virgolibra/smart_office_project/flutter_smart_office_project/assets/title1.png

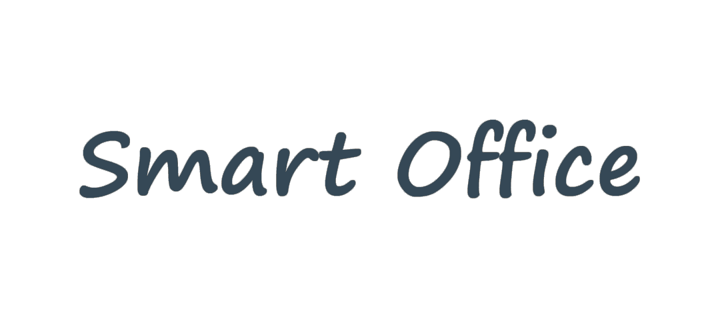
flutter_smart_office_project/assets/title1.png
