virgolibra/smart_office_project/images/Fusion/IRBoxMd1.jpg

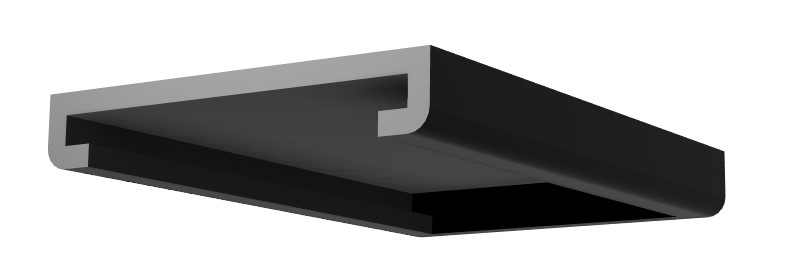
images/Fusion/IRBoxMd1.jpg
