virgolibra/smart_office_project/images/Fusion/IRBoxMd2.jpg

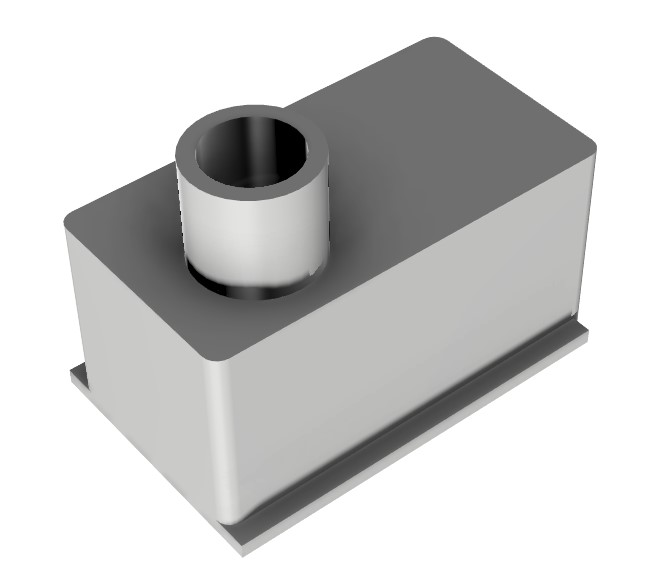
images/Fusion/IRBoxMd2.jpg
