virgolibra/smart_office_project/images/Fusion/IRBoxMd3.jpg

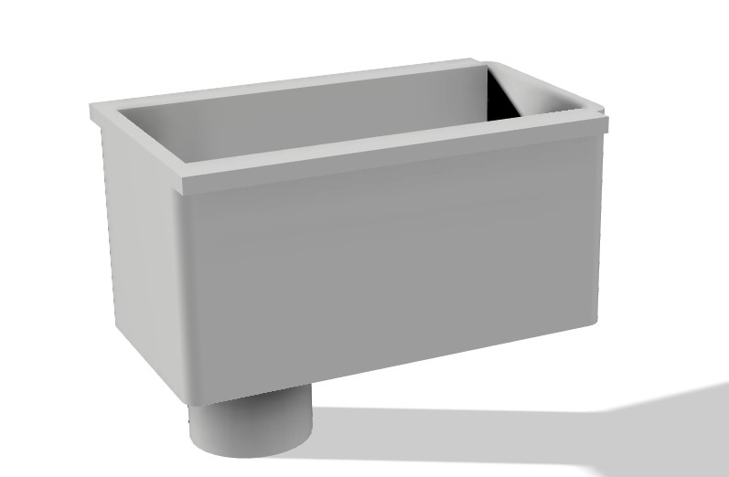
images/Fusion/IRBoxMd3.jpg
