virgolibra/smart_office_project/images/Fusion/IRBoxMd4.jpg

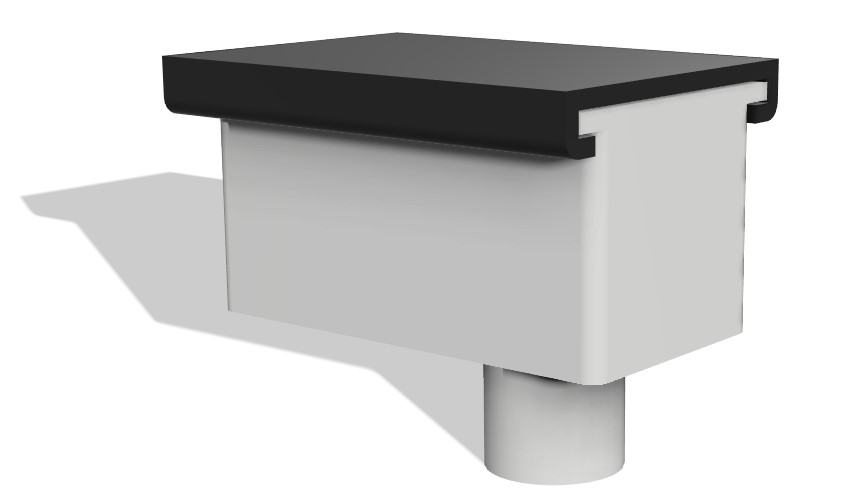
images/Fusion/IRBoxMd4.jpg
