virgolibra/smart_office_project/images/Fusion/IRBoxMd5.jpg

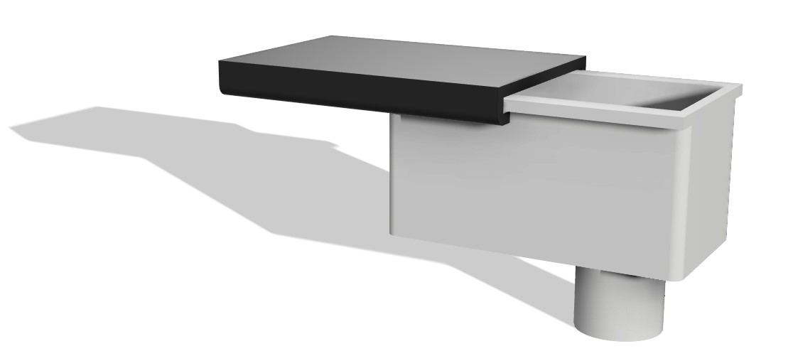
images/Fusion/IRBoxMd5.jpg
