virgolibra/smart_office_project/images/Fusion/IRBoxSd1.jpg

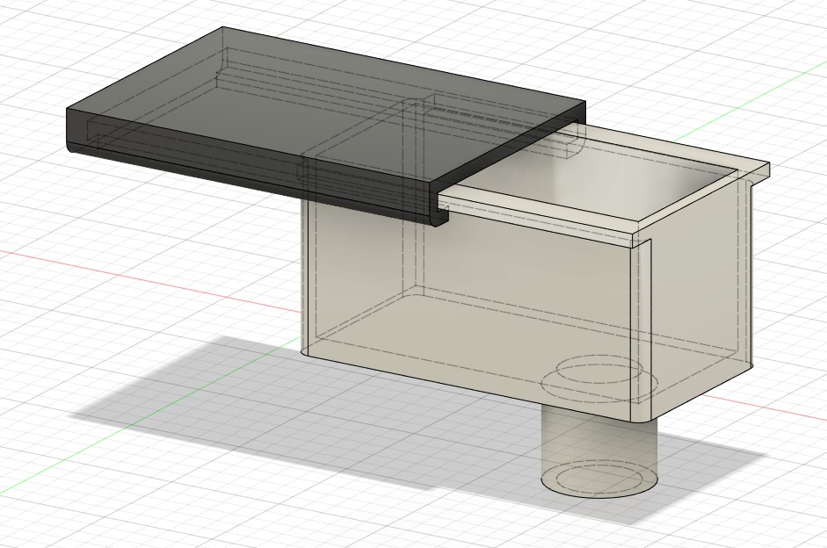
images/Fusion/IRBoxSd1.jpg
