virgolibra/smart_office_project/images/Fusion/IRBoxSk1.jpg

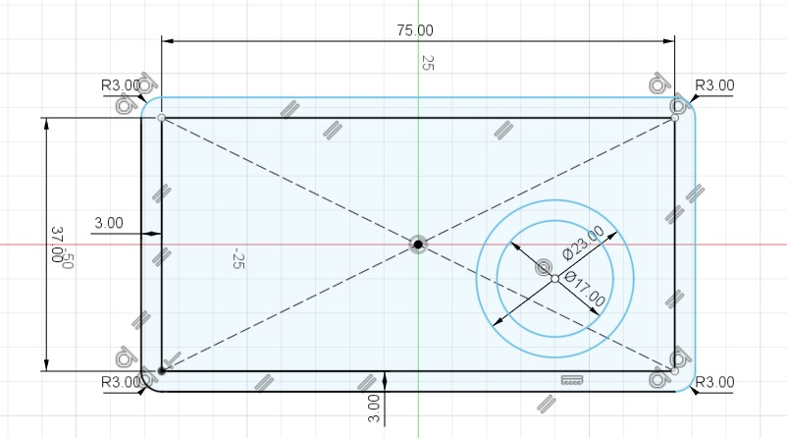
images/Fusion/IRBoxSk1.jpg
