virgolibra/smart_office_project/images/Fusion/IRBoxSk2.jpg

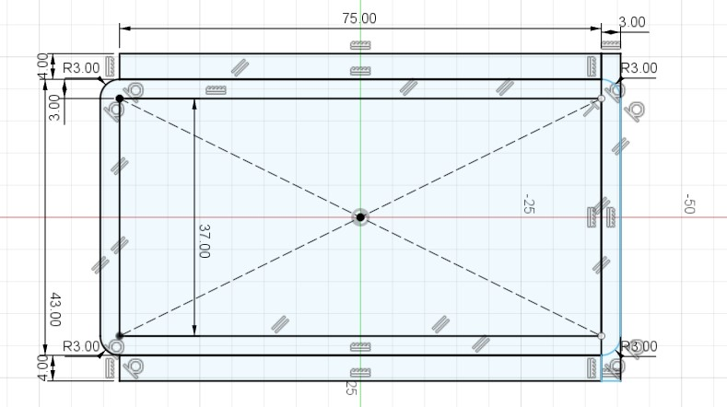
images/Fusion/IRBoxSk2.jpg
