virgolibra/smart_office_project/images/Fusion/IRBoxSk3.jpg

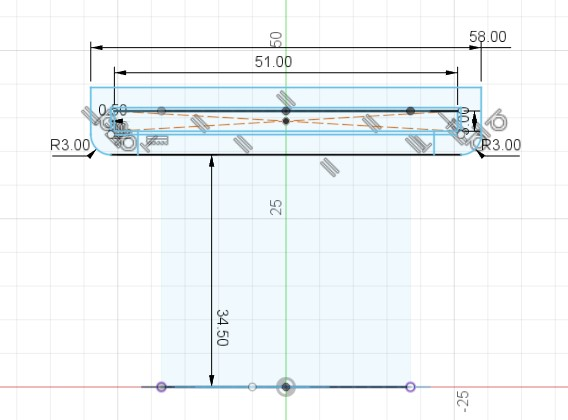
images/Fusion/IRBoxSk3.jpg
