virgolibra/smart_office_project/images/Fusion/RFID/RFIDRd1.jpg

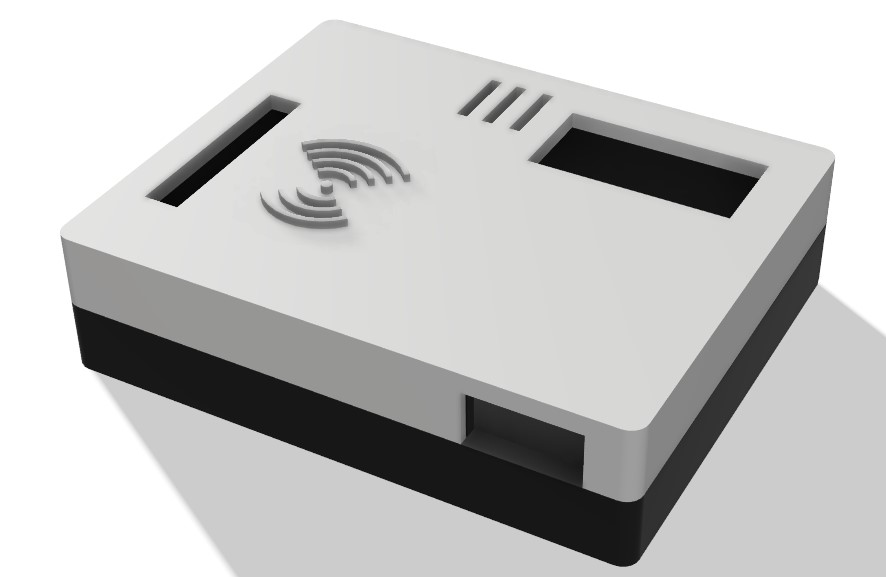
images/Fusion/RFID/RFIDRd1.jpg
