virgolibra/smart_office_project/images/Fusion/RFID/RFIDRd2.jpg

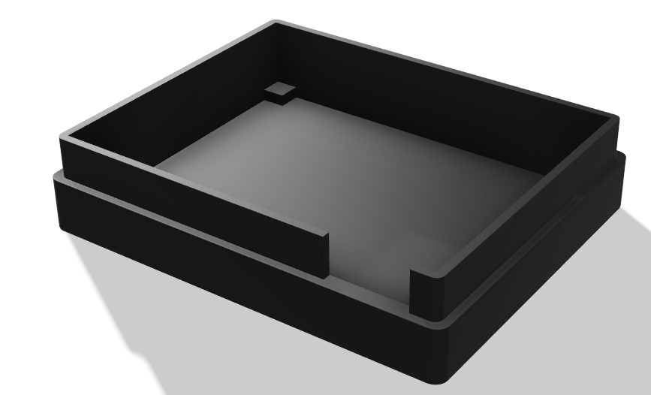
images/Fusion/RFID/RFIDRd2.jpg
