virgolibra/smart_office_project/images/Fusion/RFID/RFIDRd3.jpg

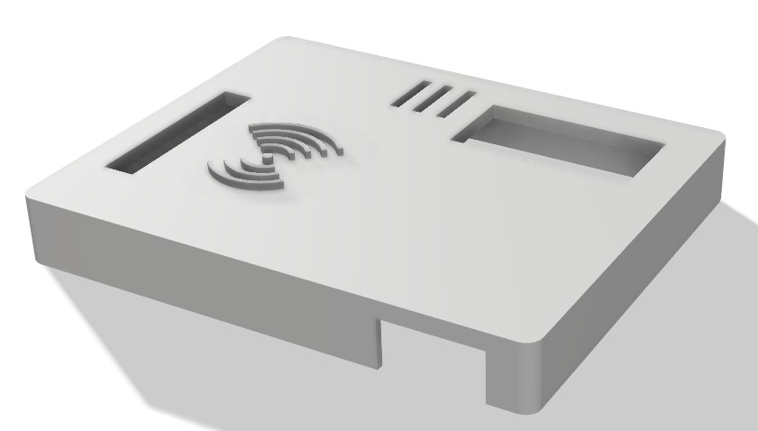
images/Fusion/RFID/RFIDRd3.jpg
