virgolibra/smart_office_project/images/Fusion/RFID/RFIDSc1.jpg

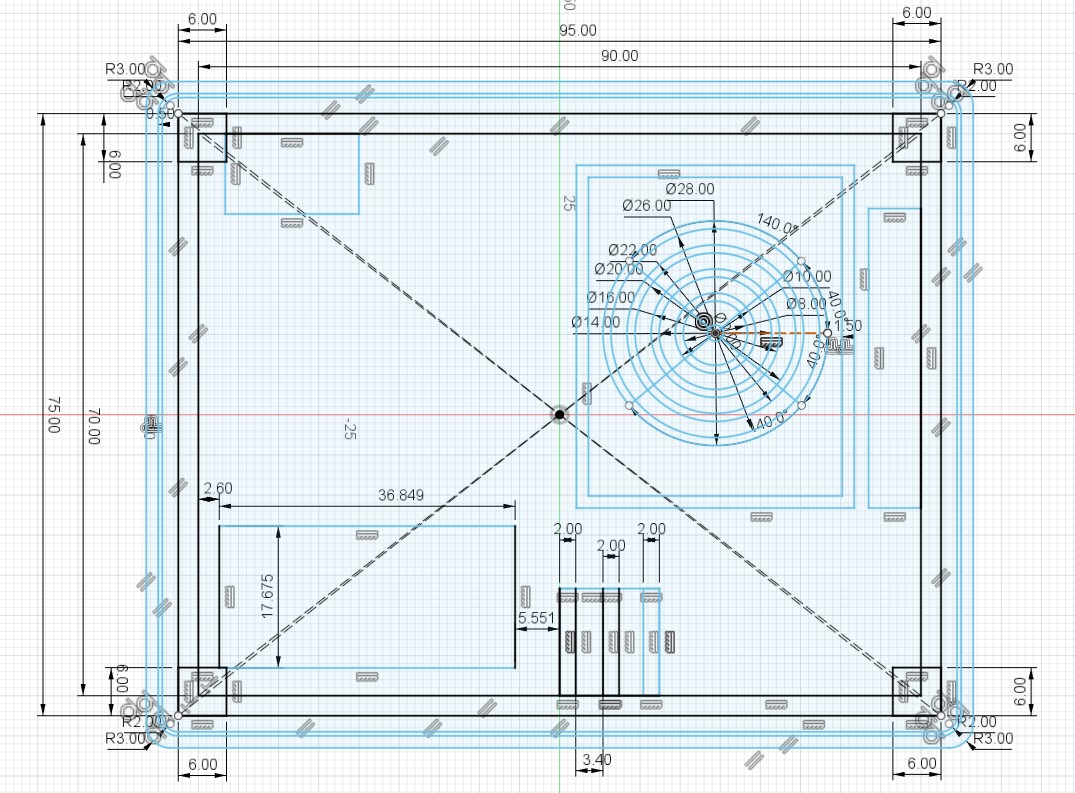
images/Fusion/RFID/RFIDSc1.jpg
