virgolibra/smart_office_project/images/Fusion/RFID/RFIDSd1.jpg

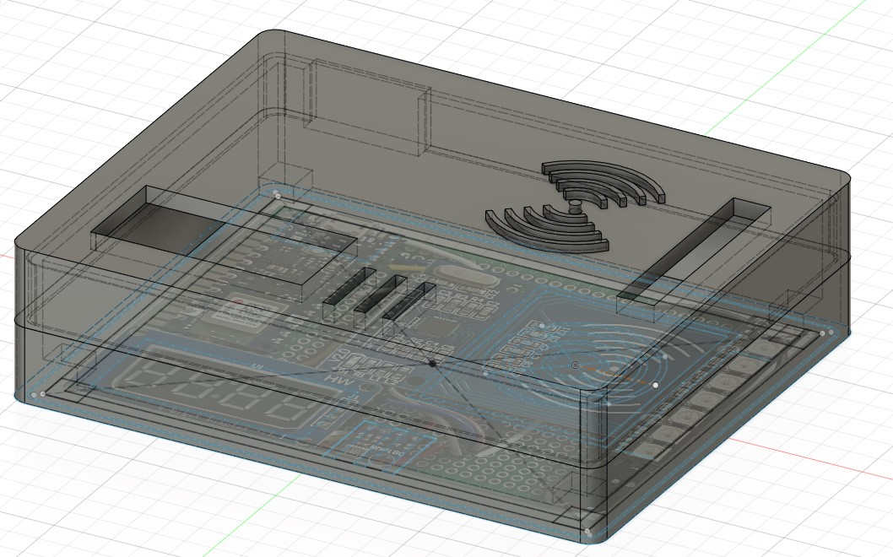
images/Fusion/RFID/RFIDSd1.jpg
