virgolibra/smart_office_project/images/Fusion/RFID/RFIDSk1.jpg

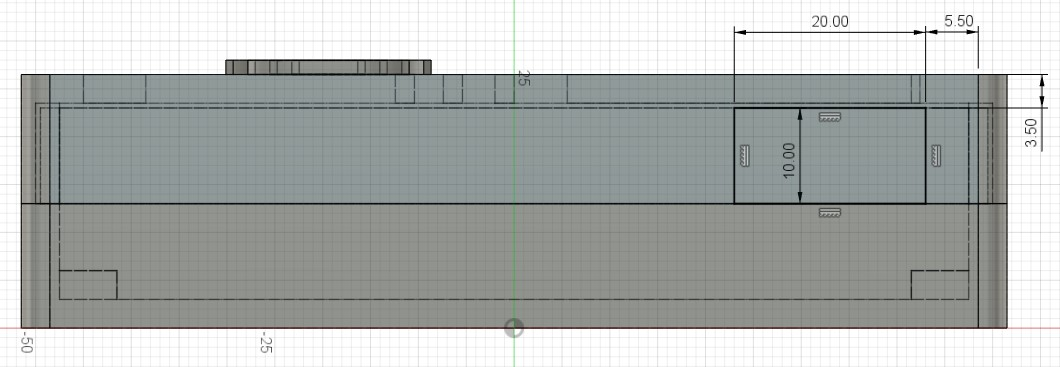
images/Fusion/RFID/RFIDSk1.jpg
